kmolski/hydrohomie/firmware/include/secrets.h

constexpr char WIFI_SSID[] = "REDACTED";
constexpr char WIFI_PASS[] = "REDACTED";

constexpr char MQTT_SERVER_IP[] = "REDACTED";
constexpr char MQTT_TOPIC[] = "REDACTED";
